vsaezen/benfica-cyd-desk-buddy/firmware/BenficaCYD/assets/aguia_vitoria_source.jpg

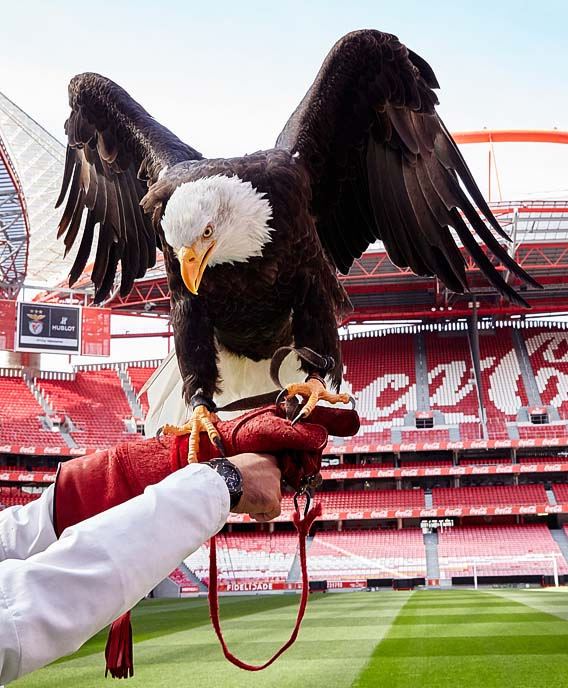
firmware/BenficaCYD/assets/aguia_vitoria_source.jpg
