vsaezen/benfica-cyd-desk-buddy/firmware/BenficaCYD/assets/eagle_flight_sheet_source.png

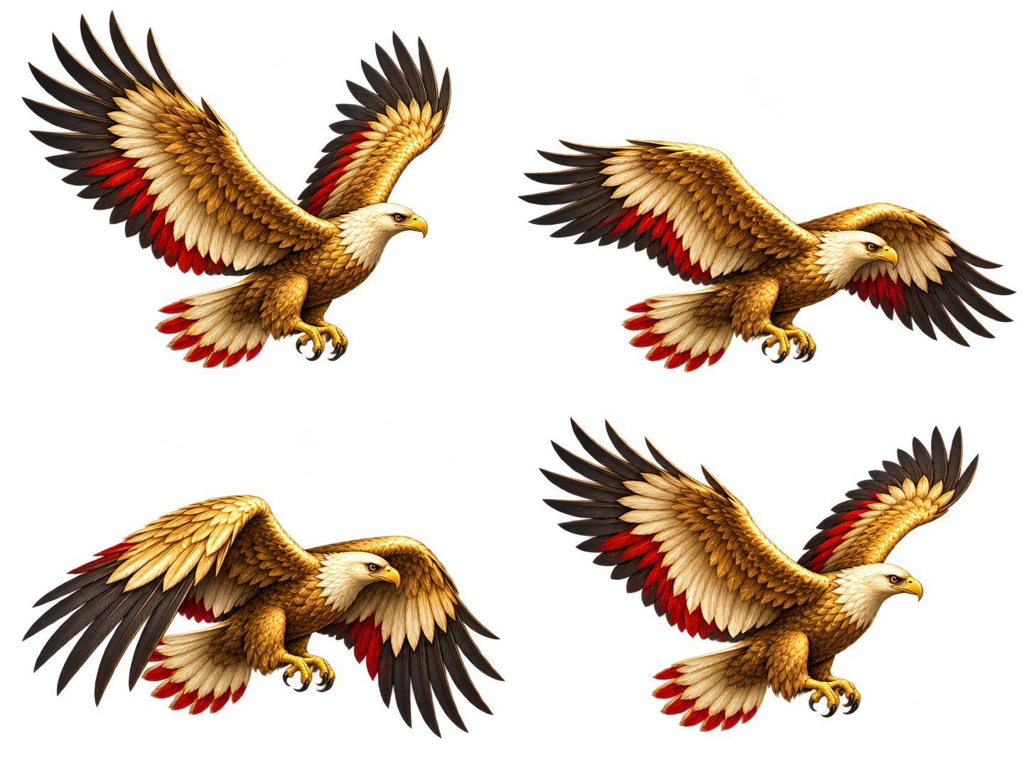
firmware/BenficaCYD/assets/eagle_flight_sheet_source.png
