vsaezen/benfica-cyd-desk-buddy/firmware/BenficaCYD/assets/papoila_source.jpg

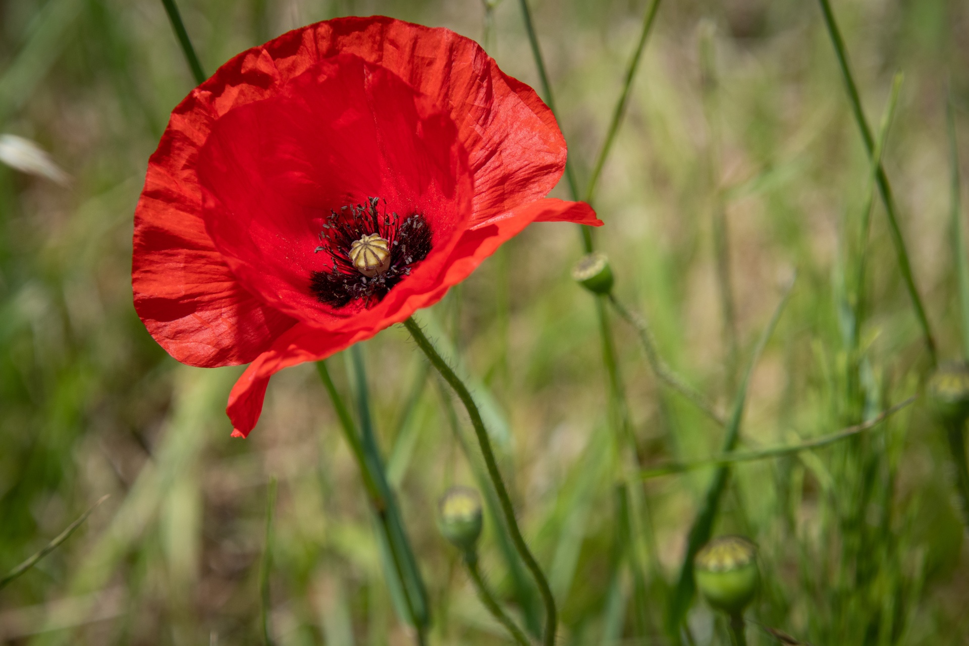
firmware/BenficaCYD/assets/papoila_source.jpg
