vsaezen/benfica-cyd-desk-buddy/firmware/BenficaCYD/BenficaFont.h

#pragma once
#include <Arduino.h>

static const uint8_t PROGMEM Graduate14Bitmaps[] = {
  0x00, 0x66, 0x66, 0x64, 0x40, 0x06, 0x79, 0x65, 0x00, 0x00, 0x00, 0x00, 0x00, 0x00, 0x00, 0x08,
  0x81, 0x10, 0xFF, 0x0C, 0xC1, 0x10, 0x22, 0x1F, 0xE1, 0x98, 0x22, 0x04, 0x40, 0x08, 0x04, 0x0F,
  0x8D, 0x66, 0x83, 0x40, 0xF8, 0x16, 0x09, 0x04, 0x9A, 0xC7, 0xC0, 0x80, 0x40, 0x00, 0x83, 0xCC,
  0x12, 0x40, 0x92, 0x04, 0xB0, 0x25, 0x79, 0xEA, 0x40, 0xD2, 0x04, 0x90, 0x24, 0x82, 0x3C, 0x10,
  0x00, 0x1E, 0x0C, 0xC2, 0x10, 0xC0, 0x79, 0x92, 0xC4, 0xE1, 0x18, 0x6F, 0x0E, 0xE0, 0x69, 0x00,
  0x00, 0x00, 0x00, 0x01, 0xCC, 0xC6, 0x31, 0x8C, 0x63, 0x18, 0xC2, 0x1C, 0x00, 0x07, 0x18, 0x63,
  0x18, 0xC6, 0x31, 0x8C, 0x62, 0x70, 0x00, 0x10, 0xA9, 0xF1, 0xC6, 0x80, 0x00, 0x00, 0x00, 0x00,
  0x00, 0x08, 0x04, 0x1F, 0xC1, 0x00, 0x80, 0x40, 0x00, 0x00, 0x49, 0x00, 0x00, 0xF8, 0x00, 0x00,
  0x00, 0x00, 0x00, 0x08, 0x00, 0x20, 0x86, 0x10, 0x42, 0x08, 0x61, 0x04, 0x30, 0x80, 0x3E, 0x31,
  0x90, 0x48, 0x24, 0x92, 0x09, 0x04, 0x82, 0x63, 0x1F, 0x00, 0x1C, 0x1E, 0x03, 0x01, 0x80, 0xC0,
  0x60, 0x30, 0x18, 0x0C, 0x1F, 0x80, 0x3E, 0x33, 0x18, 0xC0, 0x60, 0x60, 0x60, 0x60, 0x62, 0x63,
  0x3F, 0x80, 0x3E, 0x31, 0x10, 0xC0, 0x61, 0xE0, 0x18, 0x0C, 0xC6, 0x63, 0x1F, 0x00, 0x0E, 0x0F,
  0x05, 0x86, 0xC6, 0x62, 0x33, 0xFC, 0x0C, 0x06, 0x07, 0x80, 0x3F, 0x11, 0x88, 0xC4, 0x03, 0xE0,
  0x18, 0x0C, 0xC6, 0x63, 0x1F, 0x00, 0x3E, 0x31, 0x98, 0xCC, 0x07, 0xE3, 0x19, 0x8C, 0xC6, 0x63,
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
  {12867, 25, 36, 25,   0, -31}, // §
  {12980, 17, 34, 17,   0, -34}, // ¨
  {13053, 29, 34, 29,   0, -34}, // ©
  {13177, 17, 34, 17,   0, -34}, // ª
  {13250, 20, 25, 20,   0, -25}, // «
  {13313, 27, 18, 27,   0, -18}, // ¬
  {13374, 27, 32, 27,   0, -32}, // ­
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
};

static const GFXfont PROGMEM Graduate42 = {
  (uint8_t *)Graduate42Bitmaps,
  (GFXglyph *)Graduate42Glyphs,
  0x20, 0xFF, 49
};
